Bastouil/Thermocouple_aquisition_sans_fil/Banque_images/a_propos.png

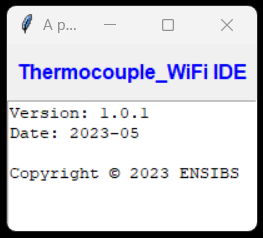
Banque_images/a_propos.png
