Bastouil/Thermocouple_aquisition_sans_fil/Banque_images/Calibrer_temperature_amb.JPG

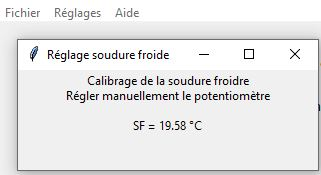
Banque_images/Calibrer_temperature_amb.JPG
