Bastouil/Thermocouple_aquisition_sans_fil/Banque_images/signal.JPG

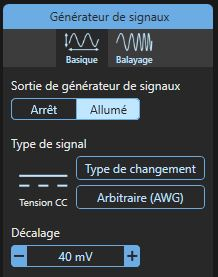
Banque_images/signal.JPG
