Bastouil/Thermocouple_aquisition_sans_fil/Banque_images/soudure_froide.png

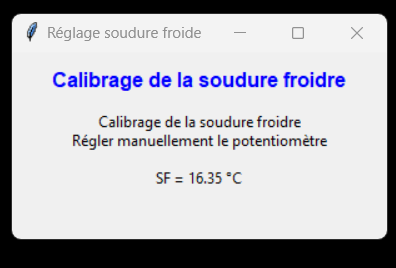
Banque_images/soudure_froide.png
