Bastouil/Thermocouple_aquisition_sans_fil/Banque_images/utilisation.png

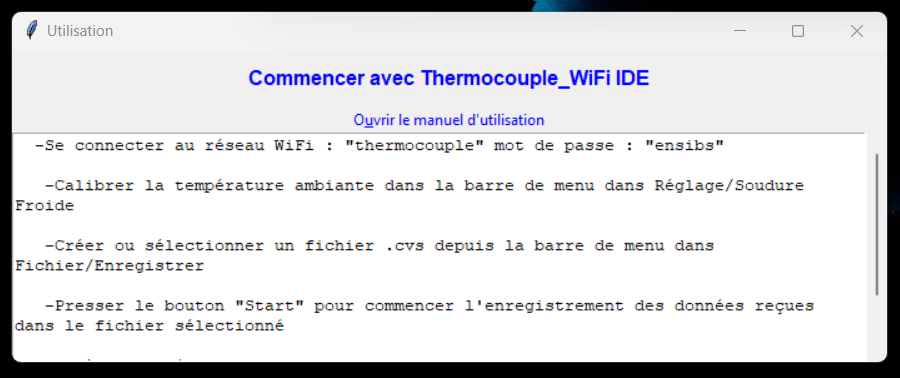
Banque_images/utilisation.png
